SRA-VJTI/MARIO/firmware/components/rosserial_esp32/include/moveit_msgs/MotionPlanDetailedResponse.h

#ifndef _ROS_moveit_msgs_MotionPlanDetailedResponse_h
#define _ROS_moveit_msgs_MotionPlanDetailedResponse_h

#include <stdint.h>
#include <string.h>
#include <stdlib.h>
#include "ros/msg.h"
#include "moveit_msgs/RobotState.h"
#include "moveit_msgs/RobotTrajectory.h"
#include "moveit_msgs/MoveItErrorCodes.h"

namespace moveit_msgs
{

  class MotionPlanDetailedResponse : public ros::Msg
  {
    public:
      typedef moveit_msgs::RobotState _trajectory_start_type;
      _trajectory_start_type trajectory_start;
      typedef const char* _group_name_type;
      _group_name_type group_name;
      uint32_t trajectory_length;
      typedef moveit_msgs::RobotTrajectory _trajectory_type;
      _trajectory_type st_trajectory;
      _trajectory_type * trajectory;
      uint32_t description_length;
      typedef char* _description_type;
      _description_type st_description;
      _description_type * description;
      uint32_t processing_time_length;
      typedef double _processing_time_type;
      _processing_time_type st_processing_time;
      _processing_time_type * processing_time;
      typedef moveit_msgs::MoveItErrorCodes _error_code_type;
      _error_code_type error_code;

    MotionPlanDetailedResponse():
      trajectory_start(),
      group_name(""),
      trajectory_length(0), trajectory(NULL),
      description_length(0), description(NULL),
      processing_time_length(0), processing_time(NULL),
      error_code()
    {
    }

    virtual int serialize(unsigned char *outbuffer) const
    {
      int offset = 0;
      offset += this->trajectory_start.serialize(outbuffer + offset);
      uint32_t length_group_name = strlen(this->group_name);
      varToArr(outbuffer + offset, length_group_name);
      offset += 4;
      memcpy(outbuffer + offset, this->group_name, length_group_name);
      offset += length_group_name;
      *(outbuffer + offset + 0) = (this->trajectory_length >> (8 * 0)) & 0xFF;
      *(outbuffer + offset + 1) = (this->trajectory_length >> (8 * 1)) & 0xFF;
      *(outbuffer + offset + 2) = (this->trajectory_length >> (8 * 2)) & 0xFF;
      *(outbuffer + offset + 3) = (this->trajectory_length >> (8 * 3)) & 0xFF;
      offset += sizeof(this->trajectory_length);
      for( uint32_t i = 0; i < trajectory_length; i++){
      offset += this->trajectory[i].serialize(outbuffer + offset);
      }
      *(outbuffer + offset + 0) = (this->description_length >> (8 * 0)) & 0xFF;
      *(outbuffer + offset + 1) = (this->description_length >> (8 * 1)) & 0xFF;
      *(outbuffer + offset + 2) = (this->description_length >> (8 * 2)) & 0xFF;
      *(outbuffer + offset + 3) = (this->description_length >> (8 * 3)) & 0xFF;
      offset += sizeof(this->description_length);
      for( uint32_t i = 0; i < description_length; i++){
      uint32_t length_descriptioni = strlen(this->description[i]);
      varToArr(outbuffer + offset, length_descriptioni);
      offset += 4;
      memcpy(outbuffer + offset, this->description[i], length_descriptioni);
      offset += length_descriptioni;
      }
      *(outbuffer + offset + 0) = (this->processing_time_length >> (8 * 0)) & 0xFF;
      *(outbuffer + offset + 1) = (this->processing_time_length >> (8 * 1)) & 0xFF;
      *(outbuffer + offset + 2) = (this->processing_time_length >> (8 * 2)) & 0xFF;
      *(outbuffer + offset + 3) = (this->processing_time_length >> (8 * 3)) & 0xFF;
      offset += sizeof(this->processing_time_length);
      for( uint32_t i = 0; i < processing_time_length; i++){
      union {
        double real;
        uint64_t base;
      } u_processing_timei;
      u_processing_timei.real = this->processing_time[i];
      *(outbuffer + offset + 0) = (u_processing_timei.base >> (8 * 0)) & 0xFF;
      *(outbuffer + offset + 1) = (u_processing_timei.base >> (8 * 1)) & 0xFF;
      *(outbuffer + offset + 2) = (u_processing_timei.base >> (8 * 2)) & 0xFF;
      *(outbuffer + offset + 3) = (u_processing_timei.base >> (8 * 3)) & 0xFF;
      *(outbuffer + offset + 4) = (u_processing_timei.base >> (8 * 4)) & 0xFF;
      *(outbuffer + offset + 5) = (u_processing_timei.base >> (8 * 5)) & 0xFF;
      *(outbuffer + offset + 6) = (u_processing_timei.base >> (8 * 6)) & 0xFF;
      *(outbuffer + offset + 7) = (u_processing_timei.base >> (8 * 7)) & 0xFF;
      offset += sizeof(this->processing_time[i]);
      }
      offset += this->error_code.serialize(outbuffer + offset);
      return offset;
    }

    virtual int deserialize(unsigned char *inbuffer)
    {
      int offset = 0;
      offset += this->trajectory_start.deserialize(inbuffer + offset);
      uint32_t length_group_name;
      arrToVar(length_group_name, (inbuffer + offset));
      offset += 4;
      for(unsigned int k= offset; k< offset+length_group_name; ++k){
          inbuffer[k-1]=inbuffer[k];
      }
      inbuffer[offset+length_group_name-1]=0;
      this->group_name = (char *)(inbuffer + offset-1);
      offset += length_group_name;
      uint32_t trajectory_lengthT = ((uint32_t) (*(inbuffer + offset))); 
      trajectory_lengthT |= ((uint32_t) (*(inbuffer + offset + 1))) << (8 * 1); 
      trajectory_lengthT |= ((uint32_t) (*(inbuffer + offset + 2))) << (8 * 2); 
      trajectory_lengthT |= ((uint32_t) (*(inbuffer + offset + 3))) << (8 * 3); 
      offset += sizeof(this->trajectory_length);
      if(trajectory_lengthT > trajectory_length)
        this->trajectory = (moveit_msgs::RobotTrajectory*)realloc(this->trajectory, trajectory_lengthT * sizeof(moveit_msgs::RobotTrajectory));
      trajectory_length = trajectory_lengthT;
      for( uint32_t i = 0; i < trajectory_length; i++){
      offset += this->st_trajectory.deserialize(inbuffer + offset);
        memcpy( &(this->trajectory[i]), &(this->st_trajectory), sizeof(moveit_msgs::RobotTrajectory));
      }
      uint32_t description_lengthT = ((uint32_t) (*(inbuffer + offset))); 
      description_lengthT |= ((uint32_t) (*(inbuffer + offset + 1))) << (8 * 1); 
      description_lengthT |= ((uint32_t) (*(inbuffer + offset + 2))) << (8 * 2); 
      description_lengthT |= ((uint32_t) (*(inbuffer + offset + 3))) << (8 * 3); 
      offset += sizeof(this->description_length);
      if(description_lengthT > description_length)
        this->description = (char**)realloc(this->description, description_lengthT * sizeof(char*));
      description_length = description_lengthT;
      for( uint32_t i = 0; i < description_length; i++){
      uint32_t length_st_description;
      arrToVar(length_st_description, (inbuffer + offset));
      offset += 4;
      for(unsigned int k= offset; k< offset+length_st_description; ++k){
          inbuffer[k-1]=inbuffer[k];
      }
      inbuffer[offset+length_st_description-1]=0;
      this->st_description = (char *)(inbuffer + offset-1);
      offset += length_st_description;
        memcpy( &(this->description[i]), &(this->st_description), sizeof(char*));
      }
      uint32_t processing_time_lengthT = ((uint32_t) (*(inbuffer + offset))); 
      processing_time_lengthT |= ((uint32_t) (*(inbuffer + offset + 1))) << (8 * 1); 
      processing_time_lengthT |= ((uint32_t) (*(inbuffer + offset + 2))) << (8 * 2); 
      processing_time_lengthT |= ((uint32_t) (*(inbuffer + offset + 3))) << (8 * 3); 
      offset += sizeof(this->processing_time_length);
      if(processing_time_lengthT > processing_time_length)
        this->processing_time = (double*)realloc(this->processing_time, processing_time_lengthT * sizeof(double));
      processing_time_length = processing_time_lengthT;
      for( uint32_t i = 0; i < processing_time_length; i++){
      union {
        double real;
        uint64_t base;
      } u_st_processing_time;
      u_st_processing_time.base = 0;
      u_st_processing_time.base |= ((uint64_t) (*(inbuffer + offset + 0))) << (8 * 0);
      u_st_processing_time.base |= ((uint64_t) (*(inbuffer + offset + 1))) << (8 * 1);
      u_st_processing_time.base |= ((uint64_t) (*(inbuffer + offset + 2))) << (8 * 2);
      u_st_processing_time.base |= ((uint64_t) (*(inbuffer + offset + 3))) << (8 * 3);
      u_st_processing_time.base |= ((uint64_t) (*(inbuffer + offset + 4))) << (8 * 4);
      u_st_processing_time.base |= ((uint64_t) (*(inbuffer + offset + 5))) << (8 * 5);
      u_st_processing_time.base |= ((uint64_t) (*(inbuffer + offset + 6))) << (8 * 6);
      u_st_processing_time.base |= ((uint64_t) (*(inbuffer + offset + 7))) << (8 * 7);
      this->st_processing_time = u_st_processing_time.real;
      offset += sizeof(this->st_processing_time);
        memcpy( &(this->processing_time[i]), &(this->st_processing_time), sizeof(double));
      }
      offset += this->error_code.deserialize(inbuffer + offset);
     return offset;
    }

    const char * getType(){ return "moveit_msgs/MotionPlanDetailedResponse"; };
    const char * getMD5(){ return "7b84c374bb2e37bdc0eba664f7636a8f"; };

  };

}
#endif
