SRA-VJTI/MARIO/firmware/1_servo_set_zero/main/main.c

#include "sra_board.h"

#define TAG "MCPWM_SERVO_CONTROL"

servo_config servo_a = {
	.servo_pin = SERVO_A,
	.min_pulse_width = CONFIG_SERVO_A_MIN_PULSEWIDTH,
	.max_pulse_width = CONFIG_SERVO_A_MAX_PULSEWIDTH,
	.max_degree = CONFIG_SERVO_A_MAX_DEGREE,
	.mcpwm_num = MCPWM_UNIT_0,
	.timer_num = MCPWM_TIMER_0,
	.gen = MCPWM_OPR_A,
};

servo_config servo_b = {
	.servo_pin = SERVO_B,
	.min_pulse_width = CONFIG_SERVO_B_MIN_PULSEWIDTH,
	.max_pulse_width = CONFIG_SERVO_B_MAX_PULSEWIDTH,
	.max_degree = CONFIG_SERVO_B_MAX_DEGREE,
	.mcpwm_num = MCPWM_UNIT_0,
	.timer_num = MCPWM_TIMER_0,
	.gen = MCPWM_OPR_B,
};

servo_config servo_c = {
	.servo_pin = SERVO_C,
	.min_pulse_width = CONFIG_SERVO_C_MIN_PULSEWIDTH,
	.max_pulse_width = CONFIG_SERVO_C_MAX_PULSEWIDTH,
	.max_degree = CONFIG_SERVO_C_MAX_DEGREE,
	.mcpwm_num = MCPWM_UNIT_0,
	.timer_num = MCPWM_TIMER_1,
	.gen = MCPWM_OPR_A,
};

servo_config servo_d = {
	.servo_pin = SERVO_D,
	.min_pulse_width = CONFIG_SERVO_D_MIN_PULSEWIDTH,
	.max_pulse_width = CONFIG_SERVO_D_MAX_PULSEWIDTH,
	.max_degree = CONFIG_SERVO_D_MAX_DEGREE,
	.mcpwm_num = MCPWM_UNIT_0,
	.timer_num = MCPWM_TIMER_1,
	.gen = MCPWM_OPR_B,
};

static void mcpwm_servo_control(void *arg)
{
	enable_servo();
#ifdef CONFIG_ENABLE_OLED
	// Initialising the OLED
	ESP_ERROR_CHECK(init_oled());
	display_logo(MARIO_LOGO);
	vTaskDelay(100);
#endif

	while (1)
	{
		set_angle_servo(&servo_a, 0);
		vTaskDelay(100);
		set_angle_servo(&servo_b, 0);
		vTaskDelay(100);
		set_angle_servo(&servo_c, 0);
		vTaskDelay(100);
		set_angle_servo(&servo_d, 0);
		vTaskDelay(100);
#ifdef CONFIG_ENABLE_OLED
		// Diplaying Servo A, Servo B, Servo C, Servo D values on OLED
		display_servo_values(read_servo(&servo_a), read_servo(&servo_b), read_servo(&servo_c), read_servo(&servo_d));
#endif
	}
}

void app_main()
{
	ESP_LOGD(TAG, "Testing servo motors\n");
	xTaskCreate(mcpwm_servo_control, "mcpwm_example_servo_control", 4096, NULL, 5, NULL);
}
