SRA-VJTI/MARIO/firmware/3_rosserial_rviz/main/main.c

#include "stdio.h"
#include "esp_serial.h"
#include "freertos/FreeRTOS.h"
#include "freertos/task.h"

void app_main(void)
{
    enable_servo();         // init gpio pwm
    rosserial_setup(); // run rosserial setup

    while (1)
    {
        rosserial_spinonce();
        vTaskDelay(100);
    }
}
