SRA-VJTI/MARIO/firmware/components/rosserial_esp32/include/octomap_msgs/Octomap.h

#ifndef _ROS_octomap_msgs_Octomap_h
#define _ROS_octomap_msgs_Octomap_h

#include <stdint.h>
#include <string.h>
#include <stdlib.h>
#include "ros/msg.h"
#include "std_msgs/Header.h"

namespace octomap_msgs
{

  class Octomap : public ros::Msg
  {
    public:
      typedef std_msgs::Header _header_type;
      _header_type header;
      typedef bool _binary_type;
      _binary_type binary;
      typedef const char* _id_type;
      _id_type id;
      typedef double _resolution_type;
      _resolution_type resolution;
      uint32_t data_length;
      typedef int8_t _data_type;
      _data_type st_data;
      _data_type * data;

    Octomap():
      header(),
      binary(0),
      id(""),
      resolution(0),
      data_length(0), data(NULL)
    {
    }

    virtual int serialize(unsigned char *outbuffer) const
    {
      int offset = 0;
      offset += this->header.serialize(outbuffer + offset);
      union {
        bool real;
        uint8_t base;
      } u_binary;
      u_binary.real = this->binary;
      *(outbuffer + offset + 0) = (u_binary.base >> (8 * 0)) & 0xFF;
      offset += sizeof(this->binary);
      uint32_t length_id = strlen(this->id);
      varToArr(outbuffer + offset, length_id);
      offset += 4;
      memcpy(outbuffer + offset, this->id, length_id);
      offset += length_id;
      union {
        double real;
        uint64_t base;
      } u_resolution;
      u_resolution.real = this->resolution;
      *(outbuffer + offset + 0) = (u_resolution.base >> (8 * 0)) & 0xFF;
      *(outbuffer + offset + 1) = (u_resolution.base >> (8 * 1)) & 0xFF;
      *(outbuffer + offset + 2) = (u_resolution.base >> (8 * 2)) & 0xFF;
      *(outbuffer + offset + 3) = (u_resolution.base >> (8 * 3)) & 0xFF;
      *(outbuffer + offset + 4) = (u_resolution.base >> (8 * 4)) & 0xFF;
      *(outbuffer + offset + 5) = (u_resolution.base >> (8 * 5)) & 0xFF;
      *(outbuffer + offset + 6) = (u_resolution.base >> (8 * 6)) & 0xFF;
      *(outbuffer + offset + 7) = (u_resolution.base >> (8 * 7)) & 0xFF;
      offset += sizeof(this->resolution);
      *(outbuffer + offset + 0) = (this->data_length >> (8 * 0)) & 0xFF;
      *(outbuffer + offset + 1) = (this->data_length >> (8 * 1)) & 0xFF;
      *(outbuffer + offset + 2) = (this->data_length >> (8 * 2)) & 0xFF;
      *(outbuffer + offset + 3) = (this->data_length >> (8 * 3)) & 0xFF;
      offset += sizeof(this->data_length);
      for( uint32_t i = 0; i < data_length; i++){
      union {
        int8_t real;
        uint8_t base;
      } u_datai;
      u_datai.real = this->data[i];
      *(outbuffer + offset + 0) = (u_datai.base >> (8 * 0)) & 0xFF;
      offset += sizeof(this->data[i]);
      }
      return offset;
    }

    virtual int deserialize(unsigned char *inbuffer)
    {
      int offset = 0;
      offset += this->header.deserialize(inbuffer + offset);
      union {
        bool real;
        uint8_t base;
      } u_binary;
      u_binary.base = 0;
      u_binary.base |= ((uint8_t) (*(inbuffer + offset + 0))) << (8 * 0);
      this->binary = u_binary.real;
      offset += sizeof(this->binary);
      uint32_t length_id;
      arrToVar(length_id, (inbuffer + offset));
      offset += 4;
      for(unsigned int k= offset; k< offset+length_id; ++k){
          inbuffer[k-1]=inbuffer[k];
      }
      inbuffer[offset+length_id-1]=0;
      this->id = (char *)(inbuffer + offset-1);
      offset += length_id;
      union {
        double real;
        uint64_t base;
      } u_resolution;
      u_resolution.base = 0;
      u_resolution.base |= ((uint64_t) (*(inbuffer + offset + 0))) << (8 * 0);
      u_resolution.base |= ((uint64_t) (*(inbuffer + offset + 1))) << (8 * 1);
      u_resolution.base |= ((uint64_t) (*(inbuffer + offset + 2))) << (8 * 2);
      u_resolution.base |= ((uint64_t) (*(inbuffer + offset + 3))) << (8 * 3);
      u_resolution.base |= ((uint64_t) (*(inbuffer + offset + 4))) << (8 * 4);
      u_resolution.base |= ((uint64_t) (*(inbuffer + offset + 5))) << (8 * 5);
      u_resolution.base |= ((uint64_t) (*(inbuffer + offset + 6))) << (8 * 6);
      u_resolution.base |= ((uint64_t) (*(inbuffer + offset + 7))) << (8 * 7);
      this->resolution = u_resolution.real;
      offset += sizeof(this->resolution);
      uint32_t data_lengthT = ((uint32_t) (*(inbuffer + offset))); 
      data_lengthT |= ((uint32_t) (*(inbuffer + offset + 1))) << (8 * 1); 
      data_lengthT |= ((uint32_t) (*(inbuffer + offset + 2))) << (8 * 2); 
      data_lengthT |= ((uint32_t) (*(inbuffer + offset + 3))) << (8 * 3); 
      offset += sizeof(this->data_length);
      if(data_lengthT > data_length)
        this->data = (int8_t*)realloc(this->data, data_lengthT * sizeof(int8_t));
      data_length = data_lengthT;
      for( uint32_t i = 0; i < data_length; i++){
      union {
        int8_t real;
        uint8_t base;
      } u_st_data;
      u_st_data.base = 0;
      u_st_data.base |= ((uint8_t) (*(inbuffer + offset + 0))) << (8 * 0);
      this->st_data = u_st_data.real;
      offset += sizeof(this->st_data);
        memcpy( &(this->data[i]), &(this->st_data), sizeof(int8_t));
      }
     return offset;
    }

    const char * getType(){ return "octomap_msgs/Octomap"; };
    const char * getMD5(){ return "9a45536b45c5e409cd49f04bb2d9999f"; };

  };

}
#endif
