SRA-VJTI/MARIO/firmware/components/rosserial_esp32/include/moveit_msgs/ConstraintEvalResult.h

#ifndef _ROS_moveit_msgs_ConstraintEvalResult_h
#define _ROS_moveit_msgs_ConstraintEvalResult_h

#include <stdint.h>
#include <string.h>
#include <stdlib.h>
#include "ros/msg.h"

namespace moveit_msgs
{

  class ConstraintEvalResult : public ros::Msg
  {
    public:
      typedef bool _result_type;
      _result_type result;
      typedef double _distance_type;
      _distance_type distance;

    ConstraintEvalResult():
      result(0),
      distance(0)
    {
    }

    virtual int serialize(unsigned char *outbuffer) const
    {
      int offset = 0;
      union {
        bool real;
        uint8_t base;
      } u_result;
      u_result.real = this->result;
      *(outbuffer + offset + 0) = (u_result.base >> (8 * 0)) & 0xFF;
      offset += sizeof(this->result);
      union {
        double real;
        uint64_t base;
      } u_distance;
      u_distance.real = this->distance;
      *(outbuffer + offset + 0) = (u_distance.base >> (8 * 0)) & 0xFF;
      *(outbuffer + offset + 1) = (u_distance.base >> (8 * 1)) & 0xFF;
      *(outbuffer + offset + 2) = (u_distance.base >> (8 * 2)) & 0xFF;
      *(outbuffer + offset + 3) = (u_distance.base >> (8 * 3)) & 0xFF;
      *(outbuffer + offset + 4) = (u_distance.base >> (8 * 4)) & 0xFF;
      *(outbuffer + offset + 5) = (u_distance.base >> (8 * 5)) & 0xFF;
      *(outbuffer + offset + 6) = (u_distance.base >> (8 * 6)) & 0xFF;
      *(outbuffer + offset + 7) = (u_distance.base >> (8 * 7)) & 0xFF;
      offset += sizeof(this->distance);
      return offset;
    }

    virtual int deserialize(unsigned char *inbuffer)
    {
      int offset = 0;
      union {
        bool real;
        uint8_t base;
      } u_result;
      u_result.base = 0;
      u_result.base |= ((uint8_t) (*(inbuffer + offset + 0))) << (8 * 0);
      this->result = u_result.real;
      offset += sizeof(this->result);
      union {
        double real;
        uint64_t base;
      } u_distance;
      u_distance.base = 0;
      u_distance.base |= ((uint64_t) (*(inbuffer + offset + 0))) << (8 * 0);
      u_distance.base |= ((uint64_t) (*(inbuffer + offset + 1))) << (8 * 1);
      u_distance.base |= ((uint64_t) (*(inbuffer + offset + 2))) << (8 * 2);
      u_distance.base |= ((uint64_t) (*(inbuffer + offset + 3))) << (8 * 3);
      u_distance.base |= ((uint64_t) (*(inbuffer + offset + 4))) << (8 * 4);
      u_distance.base |= ((uint64_t) (*(inbuffer + offset + 5))) << (8 * 5);
      u_distance.base |= ((uint64_t) (*(inbuffer + offset + 6))) << (8 * 6);
      u_distance.base |= ((uint64_t) (*(inbuffer + offset + 7))) << (8 * 7);
      this->distance = u_distance.real;
      offset += sizeof(this->distance);
     return offset;
    }

    const char * getType(){ return "moveit_msgs/ConstraintEvalResult"; };
    const char * getMD5(){ return "093643083d24f6488cb5a868bd47c090"; };

  };

}
#endif
