SRA-VJTI/MARIO/3_simulation_rviz/config/manipulator.yaml

manipulator:
    joint_state_controller:
        type: joint_state_controller/JointStateController
        publish_rate: 20

        joint_1_controller:
        type: effort_controllers/JointPositionController
        joint: joint_1
        pid: {p: 90.0, i: 0.0, d: 0.1}
    joint_2_controller:
        type: effort_controllers/JointPositionController
        joint: joint_2
        pid: {p: 50.0, i: 0.0, d: 0.5}
    joint_3_controller:
        type: effort_controllers/JointPositionController
        joint: joint_3
        pid: {p: 9.5, i: 0.1, d: 0.01}
    joint_4_controller:
        type: effort_controllers/JointPositionController
        joint: joint_4
        pid: {p: 0.1, i: 0, d: 0}
    joint_5_controller:
        type: effort_controllers/JointPositionController
        joint: joint_5
        pid: {p: 0.1, i: 0, d: 0}
